ezrec/geeetech-g2-mods/stl/jhead_lock_x2.stl

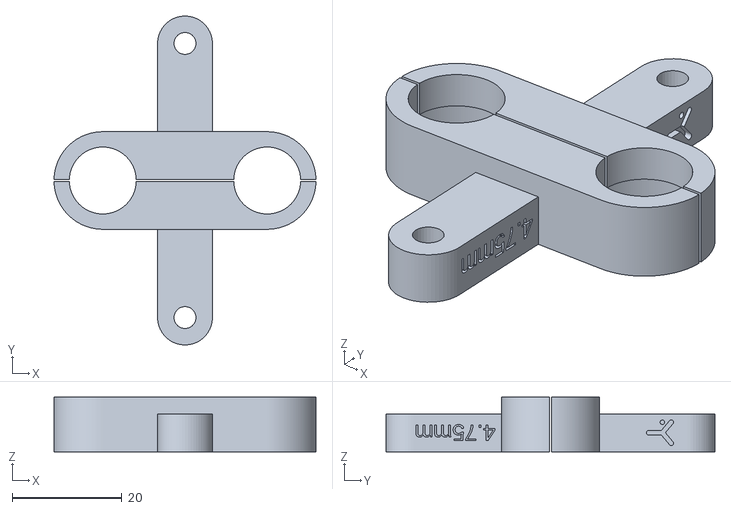
[picture p15: CAD file, 2018-11-21]
stl/jhead_lock_x2.stl
47.8 x 60.0 x 10.0
