ezrec/geeetech-g2-mods/Geeetech/RKMA-B03-FanH.STL

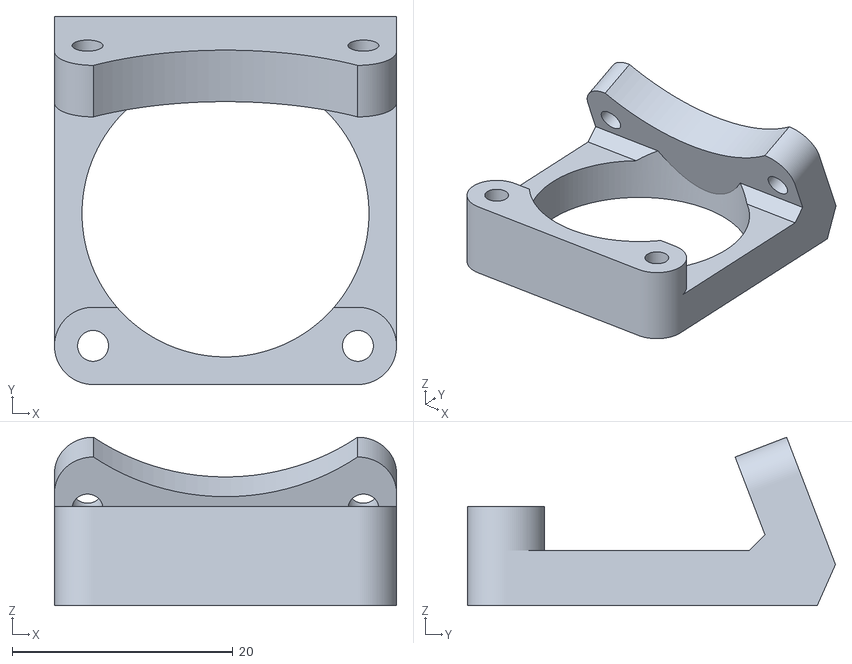
[picture p16: CAD file, 2018-11-21]
Geeetech/RKMA-B03-FanH.STL
31.0 x 33.3 x 15.3
