ezrec/geeetech-g2-mods/stl/universal_fan_duct_foot_single.stl

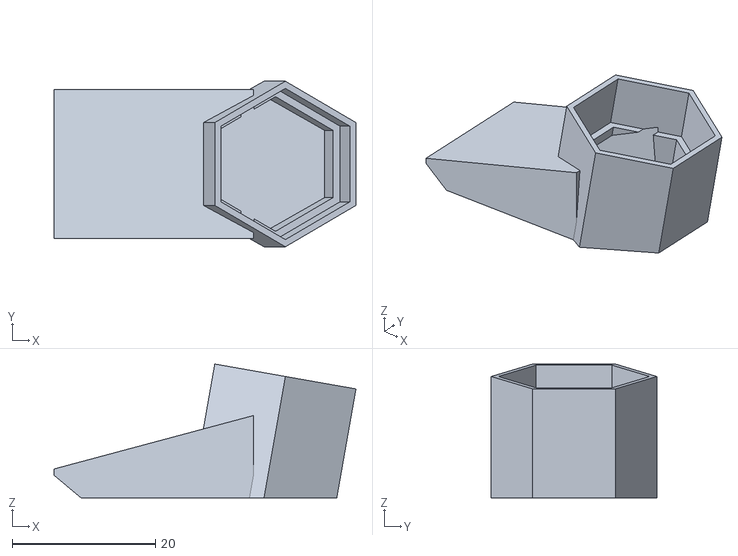
[picture p17: CAD file, 2018-11-21]
stl/universal_fan_duct_foot_single.stl
42.1 x 23.1 x 18.7
