ezrec/geeetech-g2-mods/Geeetech/rostock_g2_spider_no_probe.stl

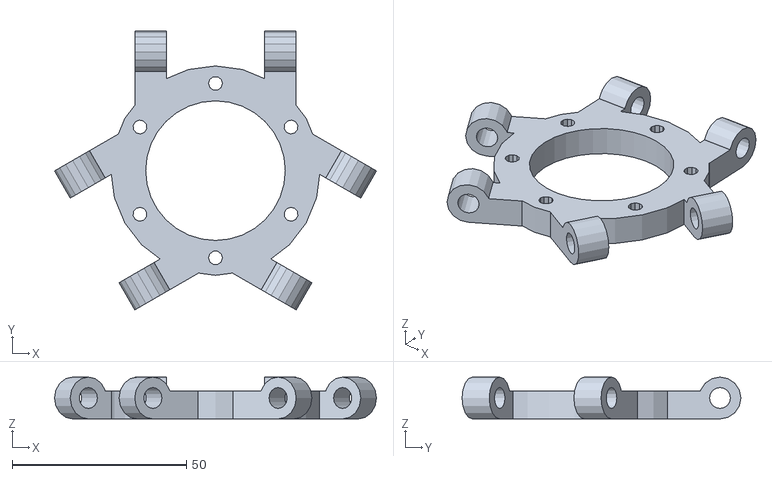
[picture p18: CAD file, 2015-09-20]
Geeetech/rostock_g2_spider_no_probe.stl
92.3 x 79.9 x 12.0
