ezrec/geeetech-g2-mods/stl/mcspider_effector.stl

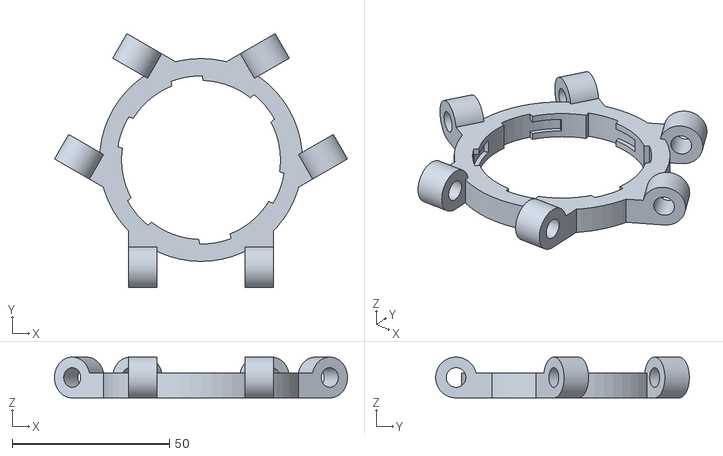
[picture p19: CAD file, 2018-11-21]
stl/mcspider_effector.stl
93.1 x 80.7 x 13.0
