ezrec/geeetech-g2-mods/stl/universal_fan_duct_foot_g2s.stl

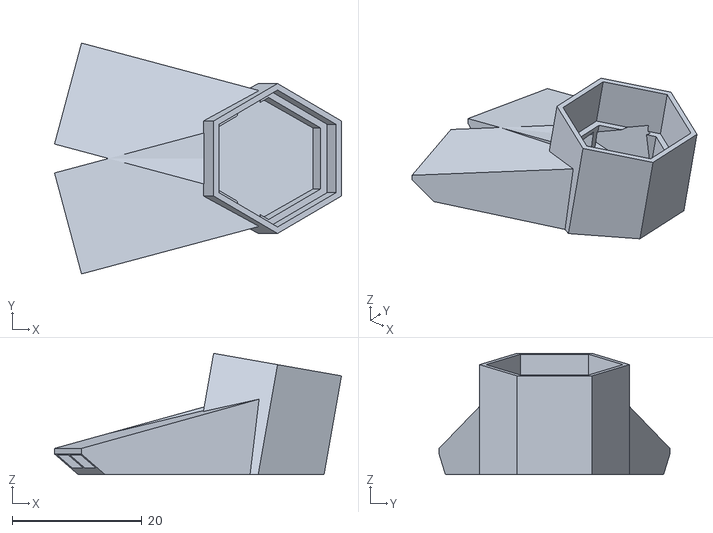
[picture p20: CAD file, 2018-11-21]
stl/universal_fan_duct_foot_g2s.stl
44.2 x 35.5 x 18.7
