ezrec/geeetech-g2-mods/stl/universal_fan_duct_clip.stl

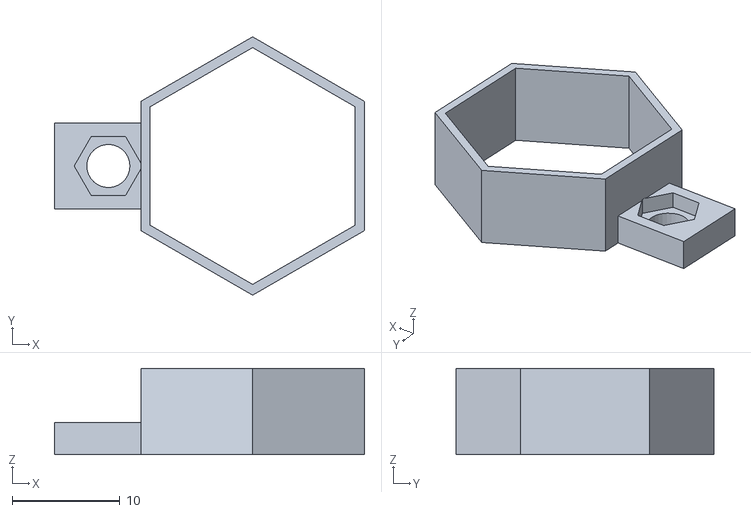
[picture p21: CAD file, 2018-11-21]
stl/universal_fan_duct_clip.stl
28.8 x 24.0 x 8.00
