ezrec/geeetech-g2-mods/stl/universal_fan_duct_blower_adapter.stl

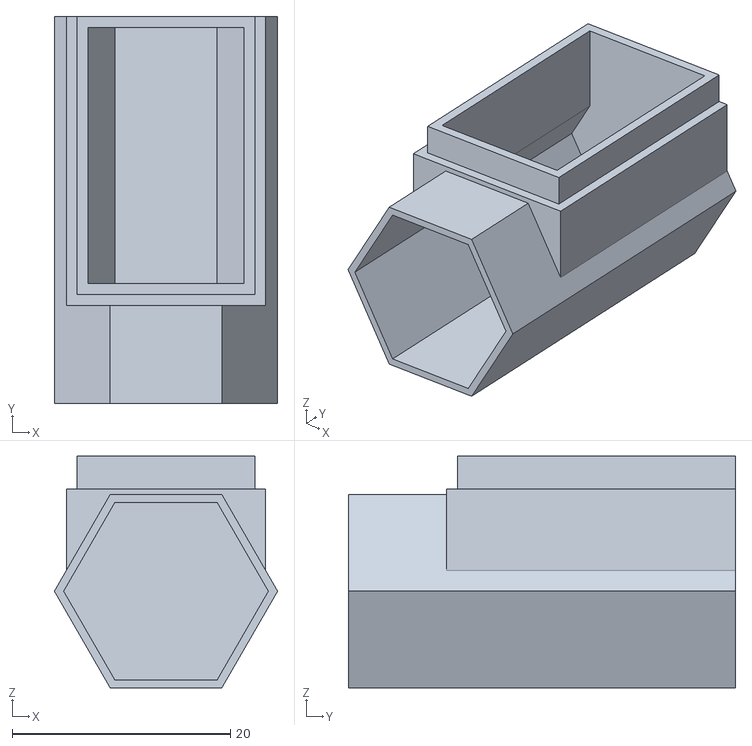
[picture p22: CAD file, 2018-11-21]
stl/universal_fan_duct_blower_adapter.stl
20.5 x 35.5 x 21.3
