ezrec/geeetech-g2-mods/stl/mcspider_lock_x2.stl

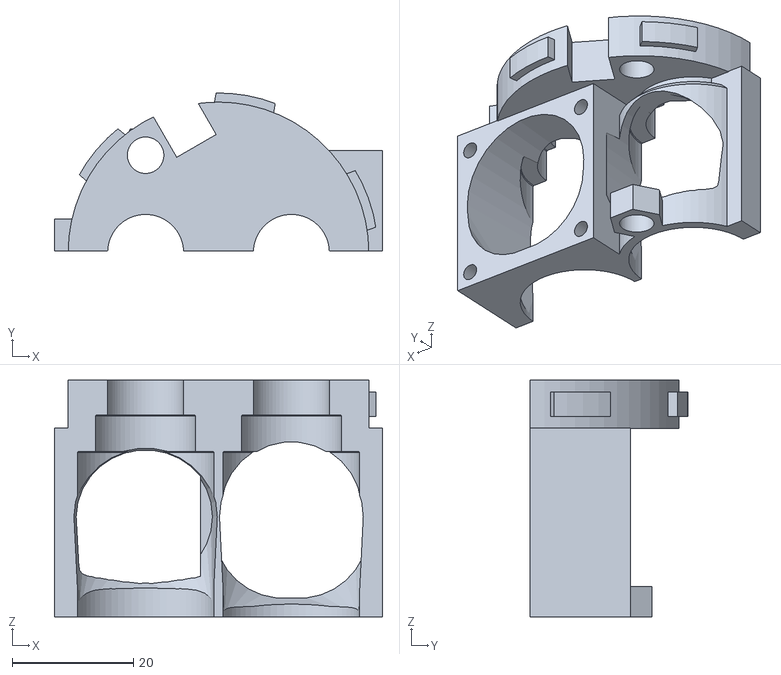
[picture p23: CAD file, 2018-11-21]
stl/mcspider_lock_x2.stl
54.0 x 26.0 x 39.0
