ezrec/geeetech-g2-mods/stl/universal_fan_duct_foot_e3d_x2.stl

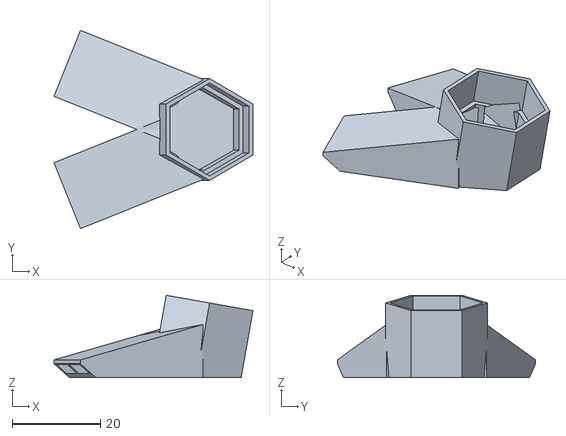
[picture p24: CAD file, 2018-11-21]
stl/universal_fan_duct_foot_e3d_x2.stl
45.1 x 44.9 x 18.7
