ezrec/geeetech-g2-mods/stl/universal_fan_duct_pipe_connector.stl

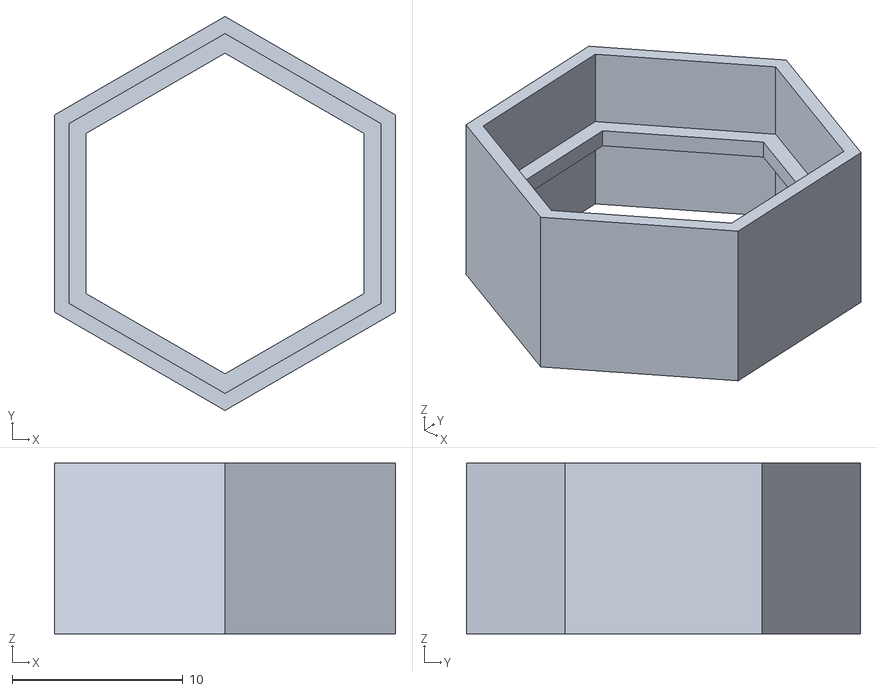
[picture p25: CAD file, 2018-11-21]
stl/universal_fan_duct_pipe_connector.stl
20.0 x 23.1 x 10.0
