ezrec/geeetech-g2-mods/stl/mk8_extruder_guide.stl

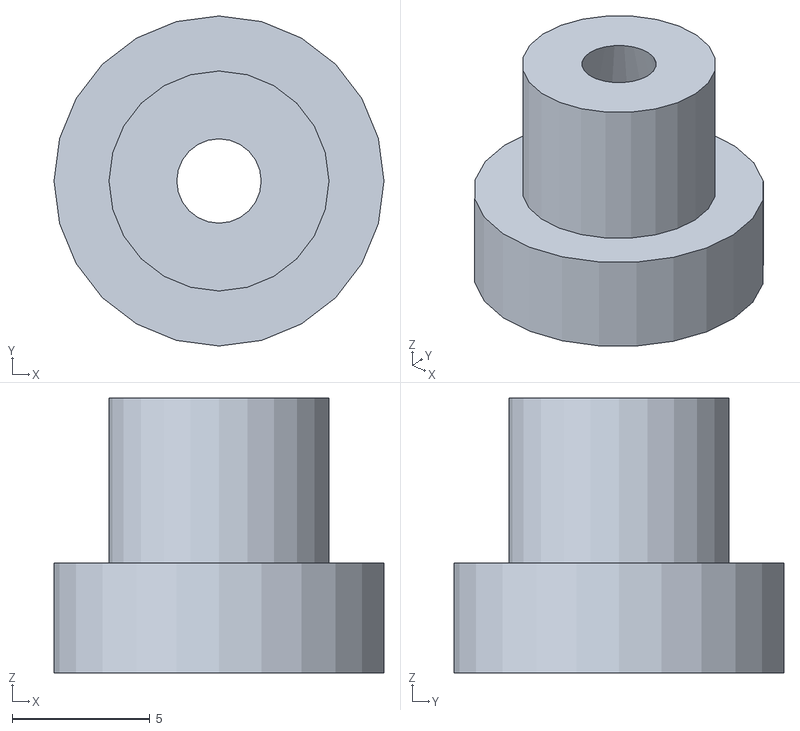
[picture p26: CAD file, 2018-11-21]
stl/mk8_extruder_guide.stl
12.0 x 12.0 x 10.0
