ezrec/geeetech-g2-mods/stl/universal_fan_duct_foot_g2s_pro.stl

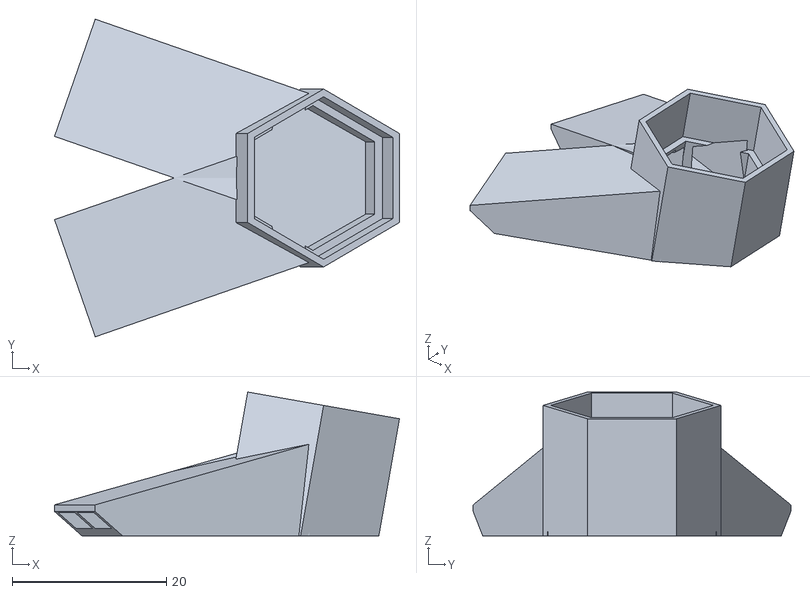
[picture p27: CAD file, 2018-11-21]
stl/universal_fan_duct_foot_g2s_pro.stl
44.7 x 41.2 x 18.7
