ezrec/geeetech-g2-mods/stl/mcspider_lock_x1_fan.stl

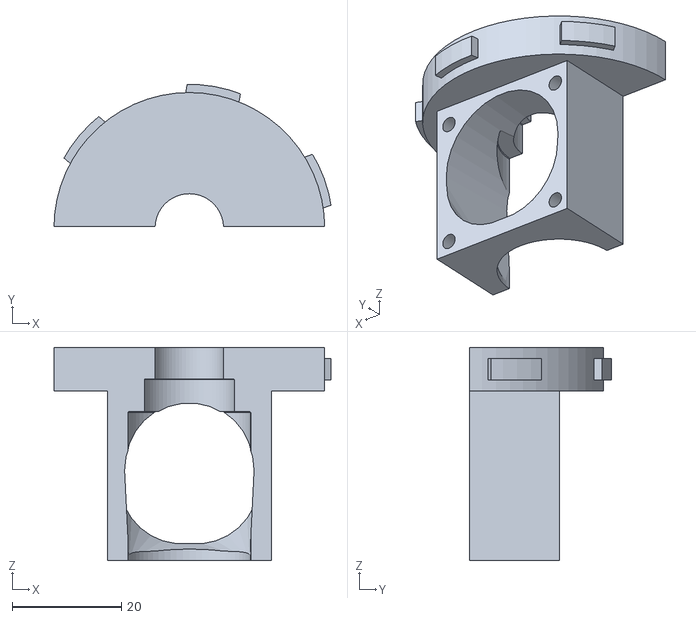
[picture p28: CAD file, 2018-11-21]
stl/mcspider_lock_x1_fan.stl
50.6 x 26.0 x 39.0
