ezrec/geeetech-g2-mods/stl/universal_spider.stl

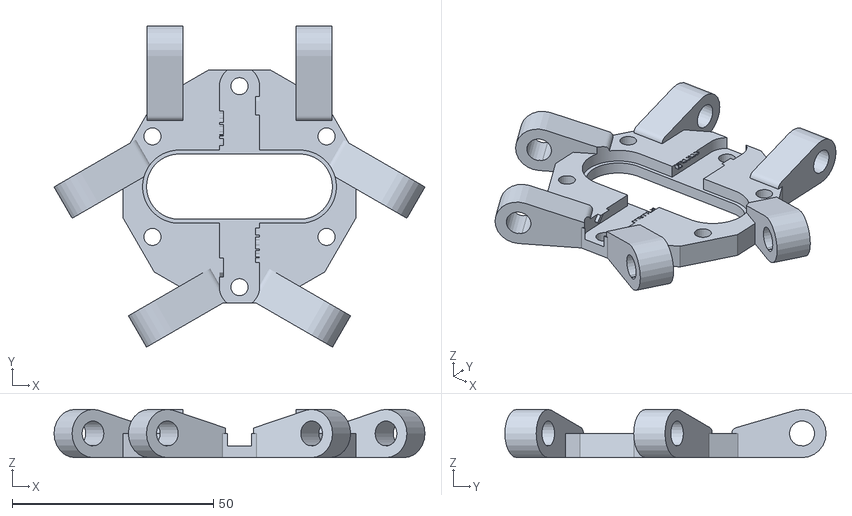
[picture p29: CAD file, 2018-11-21]
stl/universal_spider.stl
92.3 x 79.9 x 12.0
