ezrec/geeetech-g2-mods/stl/mcspider_lock_x1_foot.stl

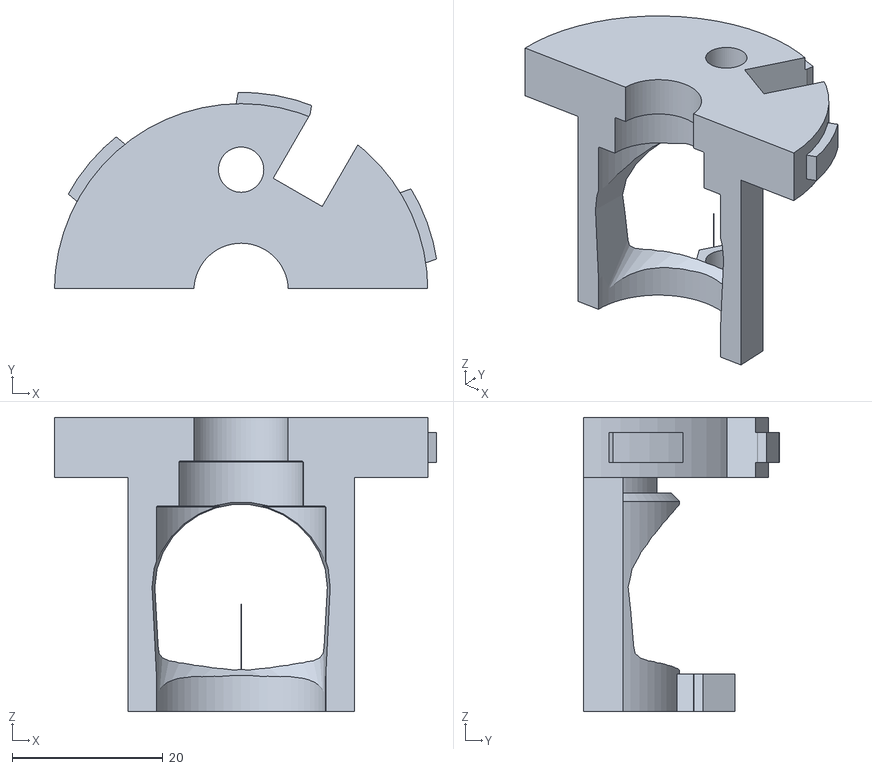
[picture p30: CAD file, 2018-11-21]
stl/mcspider_lock_x1_foot.stl
50.6 x 26.0 x 39.0
