ezrec/geeetech-g2-mods/stl/e3d_v6_lock_x1.stl

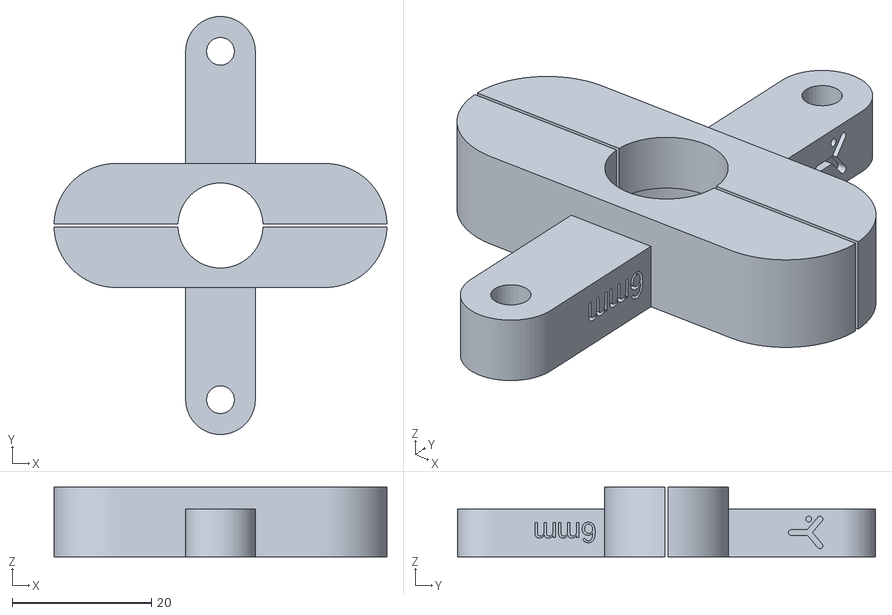
[picture p31: CAD file, 2018-11-21]
stl/e3d_v6_lock_x1.stl
47.8 x 60.0 x 10.0
