ezrec/geeetech-g2-mods/stl/mcspider_foot.stl

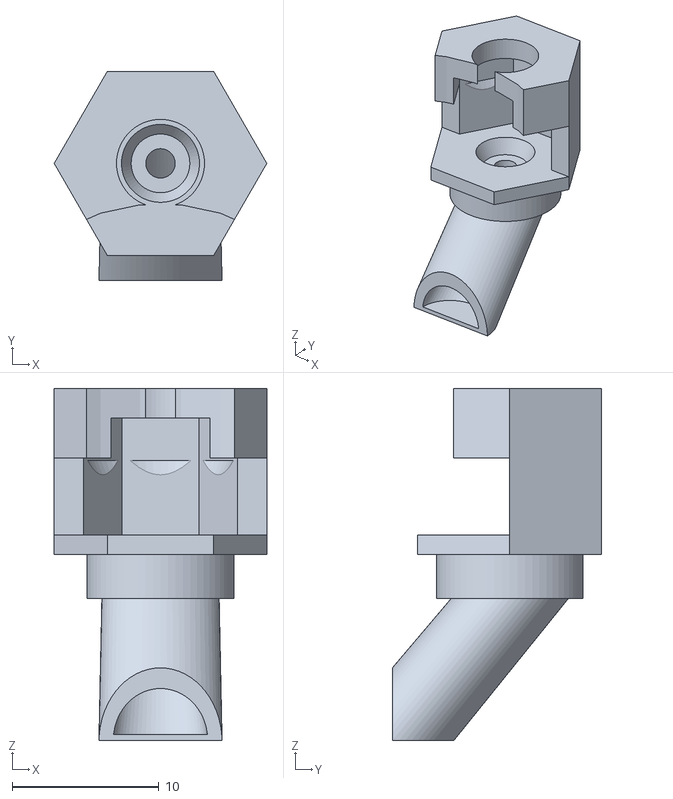
[picture p32: CAD file, 2018-11-21]
stl/mcspider_foot.stl
14.5 x 14.3 x 24.0
