ezrec/geeetech-g2-mods/stl/universal_fan_duct_pipe.stl

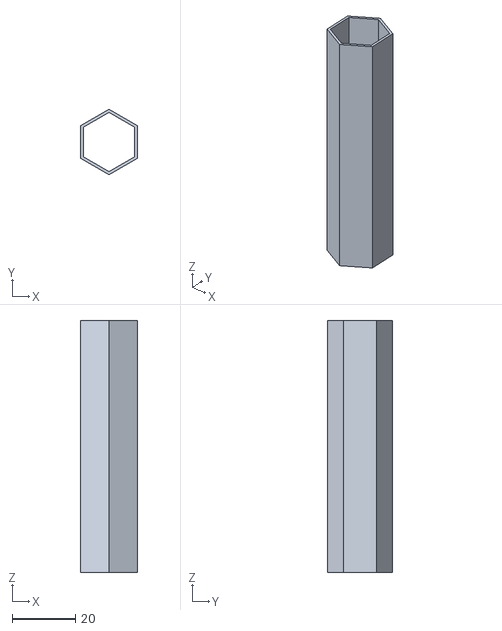
[picture p33: CAD file, 2018-11-21]
stl/universal_fan_duct_pipe.stl
18.0 x 20.8 x 80.0
