ezrec/geeetech-g2-mods/stl/geeetech_rostock_pro_spider.stl

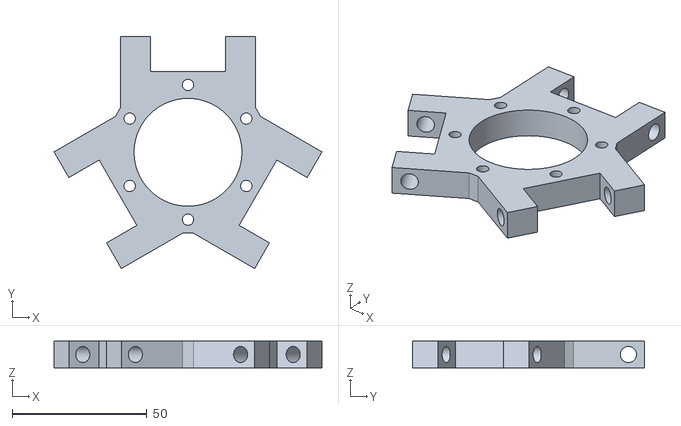
[picture p34: CAD file, 2018-11-21]
stl/geeetech_rostock_pro_spider.stl
99.5 x 86.2 x 10.0
