ezrec/geeetech-g2-mods/stl/universal_fan_duct_22mm_connector.stl

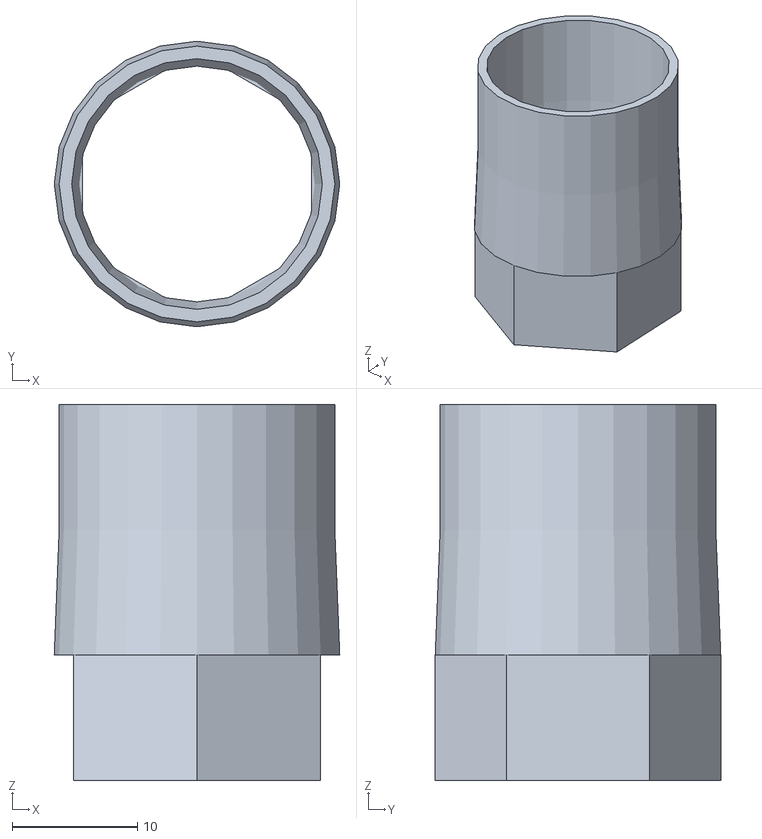
[picture p35: CAD file, 2018-11-21]
stl/universal_fan_duct_22mm_connector.stl
22.8 x 22.8 x 30.0
