ezrec/geeetech-g2-mods/stl/rod_end_shim.stl

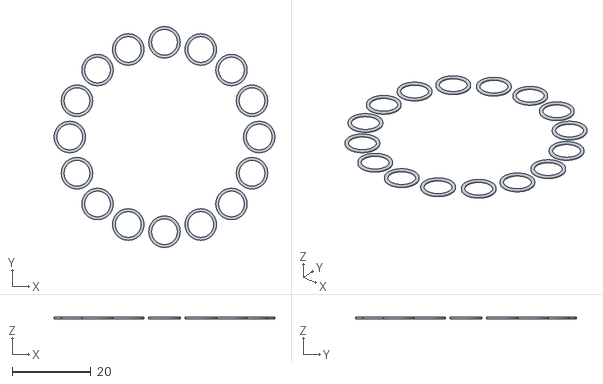
[picture p36: CAD file, 2018-11-21]
stl/rod_end_shim.stl
56.0 x 56.0 x 0.4
