ezrec/geeetech-g2-mods/stl/universal_spider_plate.stl

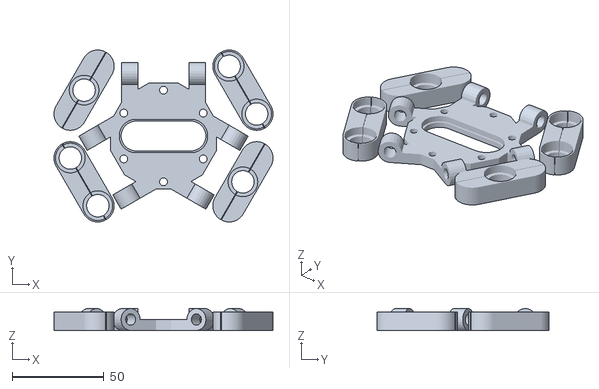
[picture p37: CAD file, 2015-12-30]
stl/universal_spider_plate.stl
119.4 x 93.8 x 12.0
